djoamersfoort/adjustable-soldering-iron/3D models/Case/Baseplate/Baseplate.png

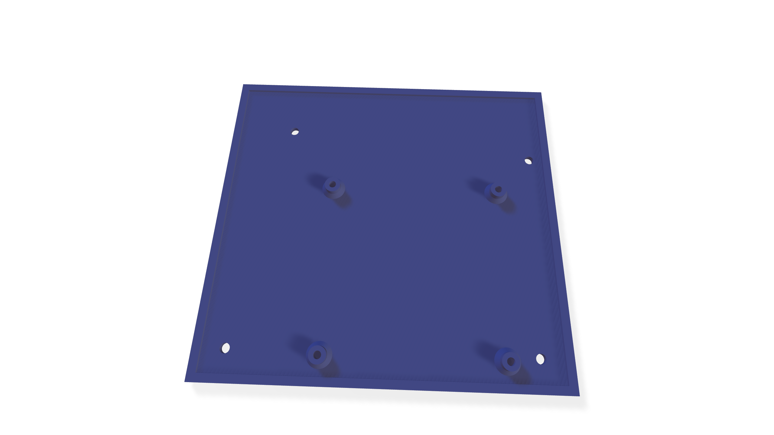
3D models/Case/Baseplate/Baseplate.png
