djoamersfoort/adjustable-soldering-iron/3D models/Case/Feet/Feet-one.png

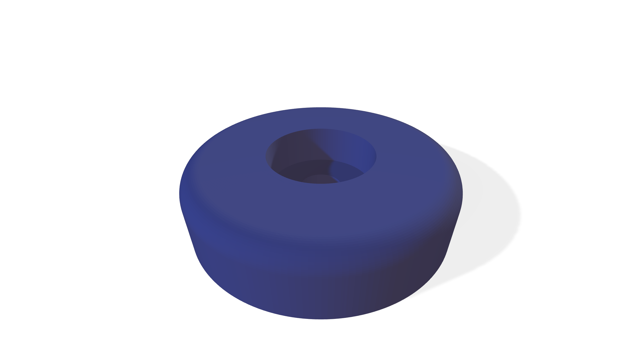
3D models/Case/Feet/Feet-one.png
