djoamersfoort/adjustable-soldering-iron/3D models/Case/IEC320-backplate-for-woodpanels-large/IEC320 backplate-for woodpanels-large.png

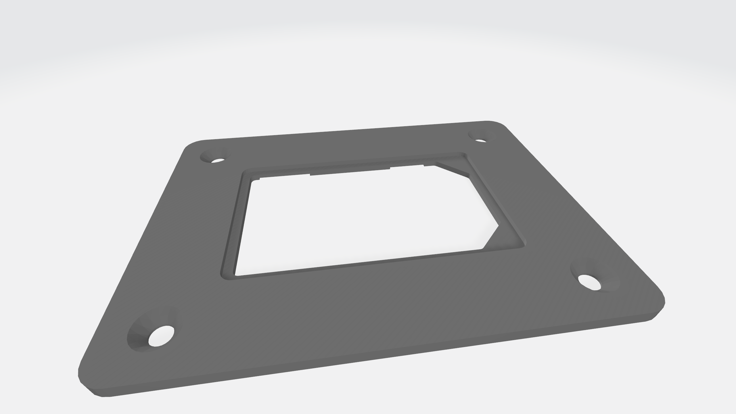
3D models/Case/IEC320-backplate-for-woodpanels-large/IEC320 backplate-for woodpanels-large.png
