djoamersfoort/adjustable-soldering-iron/3D models/Case/Standoff/Standoff-one.png

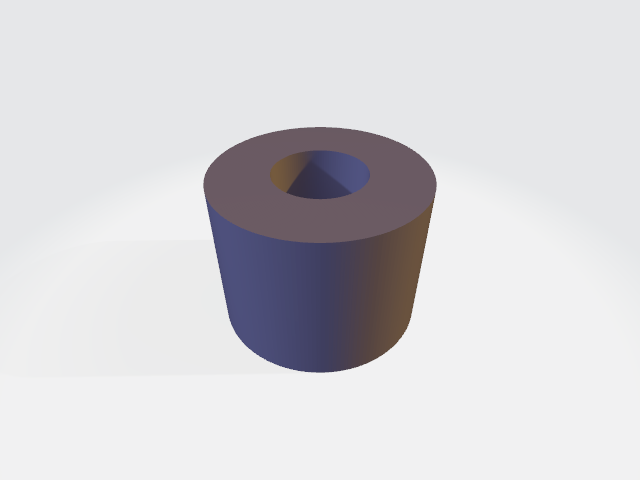
3D models/Case/Standoff/Standoff-one.png
