djoamersfoort/adjustable-soldering-iron/3D models/Parts/4-digit Display/4-digit Display.png

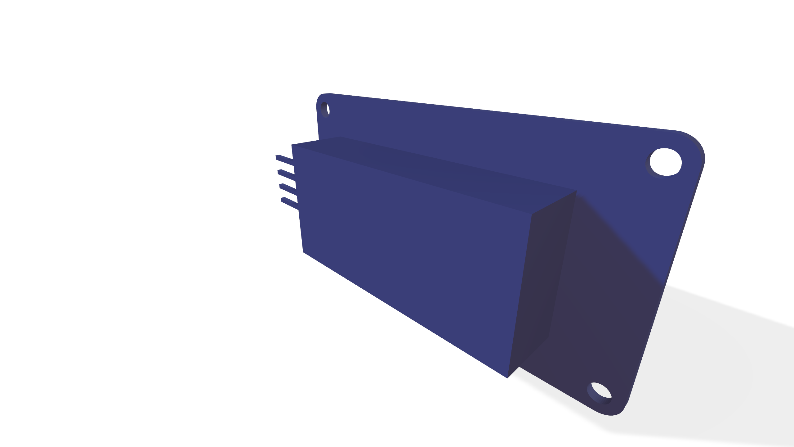
3D models/Parts/4-digit Display/4-digit Display.png
