djoamersfoort/adjustable-soldering-iron/3D models/Parts/LM2596 Place holder/LM2596 Place holder2.JPG

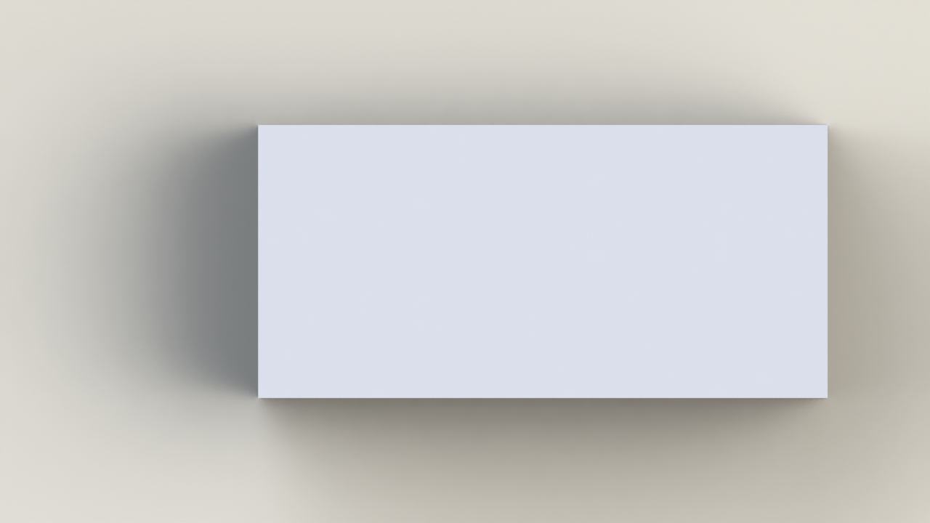
3D models/Parts/LM2596 Place holder/LM2596 Place holder2.JPG
