djoamersfoort/adjustable-soldering-iron/3D models/Parts/LM2596 Place holder/LM2596 Place holder.png

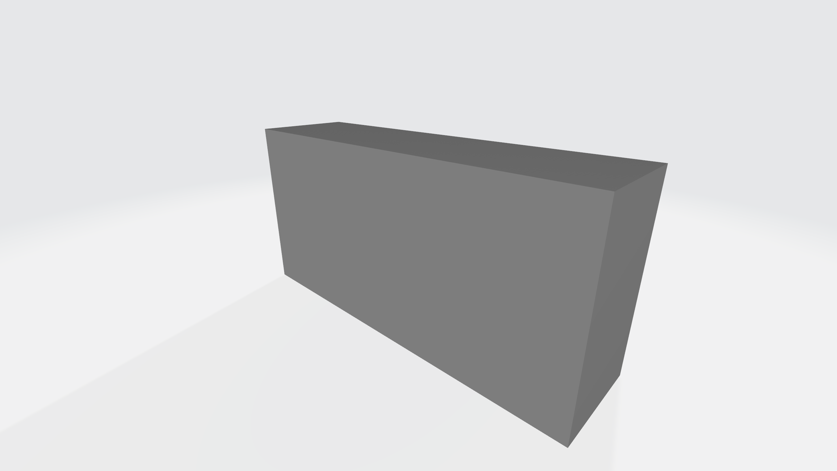
3D models/Parts/LM2596 Place holder/LM2596 Place holder.png
