djoamersfoort/adjustable-soldering-iron/3D models/Parts/MAX6675-K/MAX6675-K.JPG

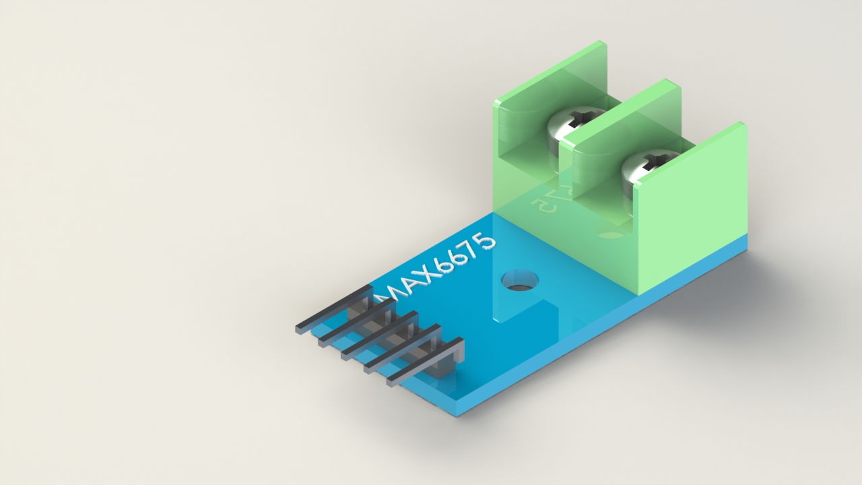
3D models/Parts/MAX6675-K/MAX6675-K.JPG
