djoamersfoort/adjustable-soldering-iron/3D models/Parts/Rotary Encoder/Rotary-Encoder2.JPG

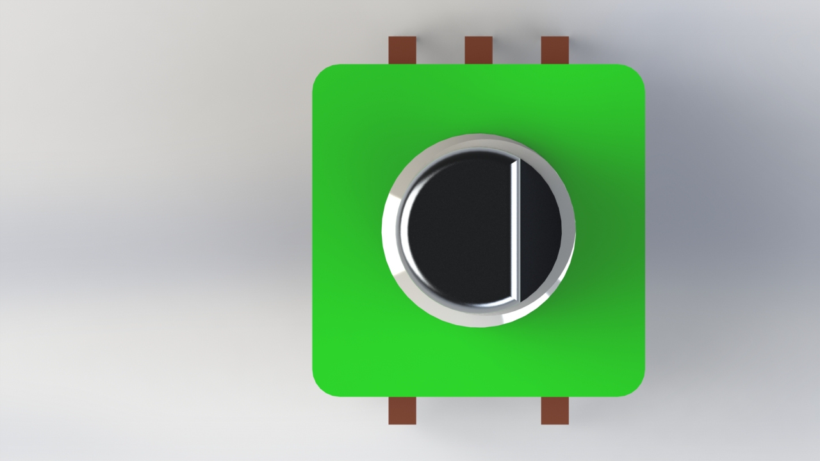
3D models/Parts/Rotary Encoder/Rotary-Encoder2.JPG
