djoamersfoort/adjustable-soldering-iron/3D models/Parts/Rotary Encoder/Rotary-Encoder.JPG

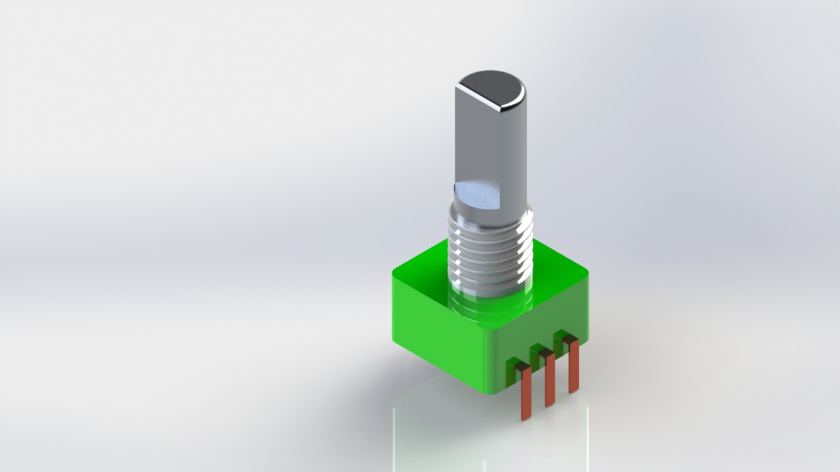
3D models/Parts/Rotary Encoder/Rotary-Encoder.JPG
