djoamersfoort/adjustable-soldering-iron/Box/BoxFront.dxf

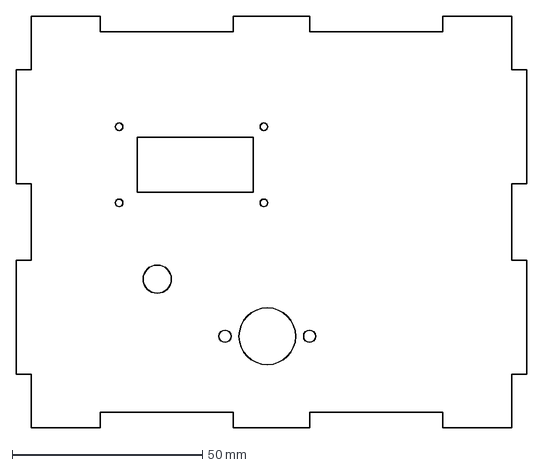
[picture p42: CAD file, 2020-01-24]
Box/BoxFront.dxf
134.0 x 108.0 mm
