djoamersfoort/adjustable-soldering-iron/3D models/Case/Baseplate/Baseplate.stl

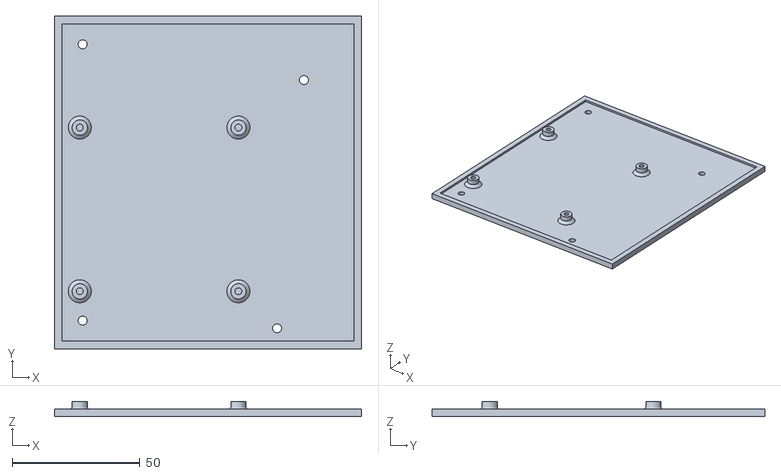
[picture p43: CAD file, 2019-11-08]
3D models/Case/Baseplate/Baseplate.stl
120.0 x 130.0 x 6.00
