djoamersfoort/adjustable-soldering-iron/3D models/Parts/4-digit Display/STEP/STEP Separate parts/Header-Base.STEP

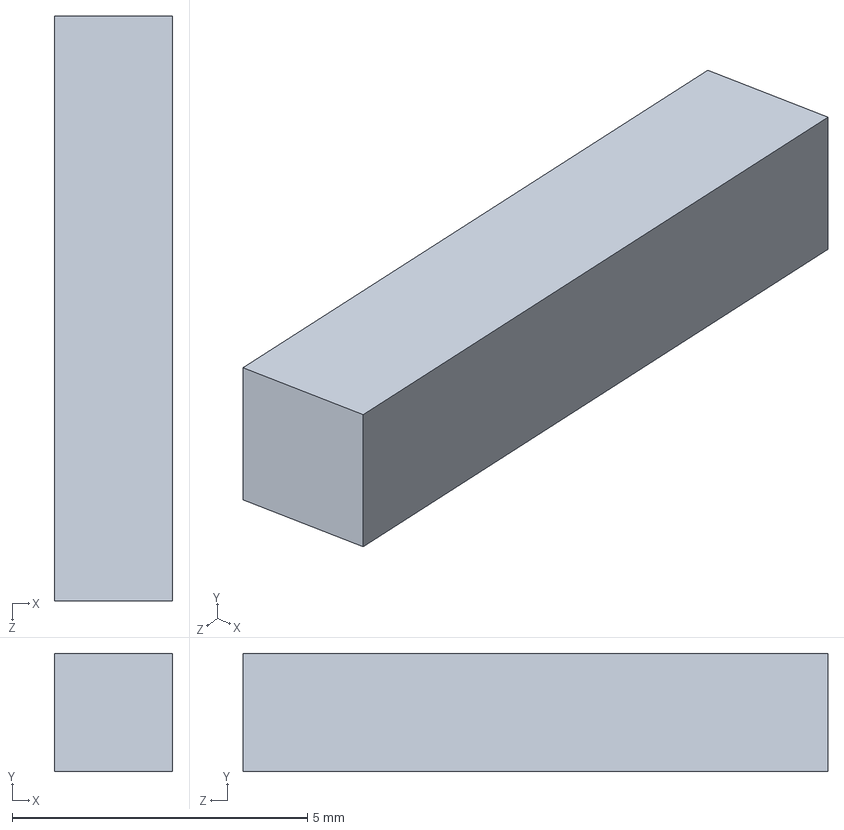
[picture p44: CAD file, 2019-11-08]
3D models/Parts/4-digit Display/STEP/STEP Separate parts/Header-Base.STEP
2.00 x 2.00 x 9.90 mm
