djoamersfoort/adjustable-soldering-iron/3D models/Parts/Rotary Encoder/STEP/STEP Separate parts/Rotary-Encoder knop.STEP

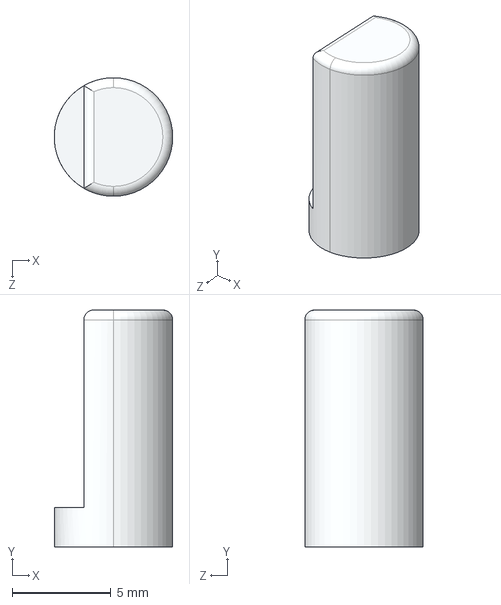
[picture p45: CAD file, 2019-11-08]
3D models/Parts/Rotary Encoder/STEP/STEP Separate parts/Rotary-Encoder knop.STEP
6.00 x 12.0 x 6.00 mm
