djoamersfoort/adjustable-soldering-iron/Box/BoxLeft.dxf

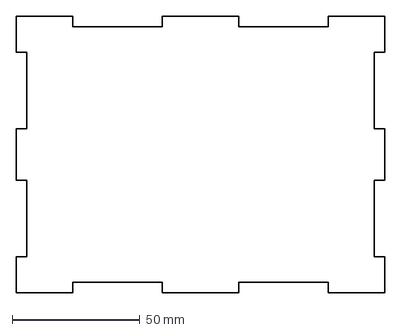
[picture p46: CAD file, 2020-01-24]
Box/BoxLeft.dxf
144.0 x 108.0 mm
