djoamersfoort/adjustable-soldering-iron/3D models/Parts/MAX6675-K/STEP/STEP Separate parts/MAX6675-K PCB.STEP

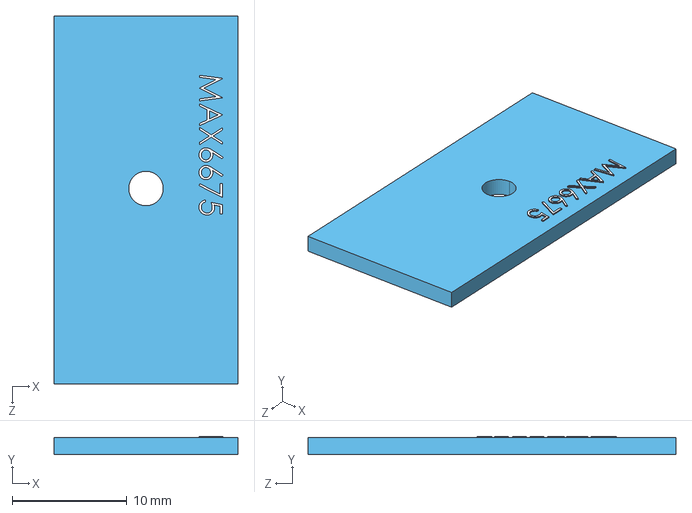
[picture p47: CAD file, 2019-11-08]
3D models/Parts/MAX6675-K/STEP/STEP Separate parts/MAX6675-K PCB.STEP
16.0 x 1.60 x 32.0 mm
