djoamersfoort/adjustable-soldering-iron/3D models/Parts/PSU/STEP/STEP Separate parts/conntectorblock.STEP

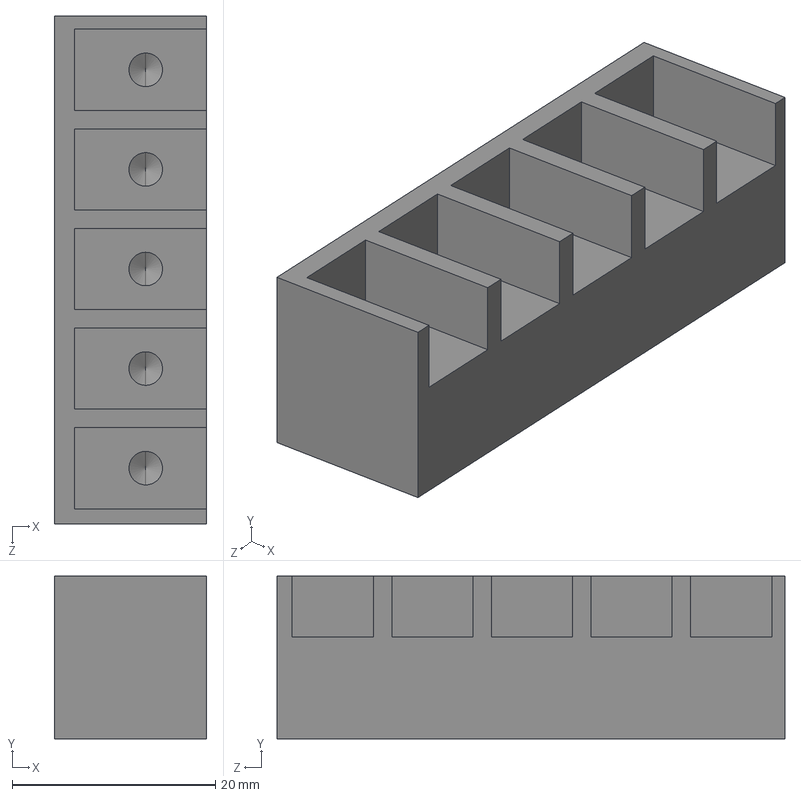
[picture p48: CAD file, 2019-11-08]
3D models/Parts/PSU/STEP/STEP Separate parts/conntectorblock.STEP
15.0 x 16.0 x 50.0 mm
