djoamersfoort/adjustable-soldering-iron/3D models/Parts/Rotary Encoder/STEP/STEP Separate parts/Rotary-Encoder Pin.STEP

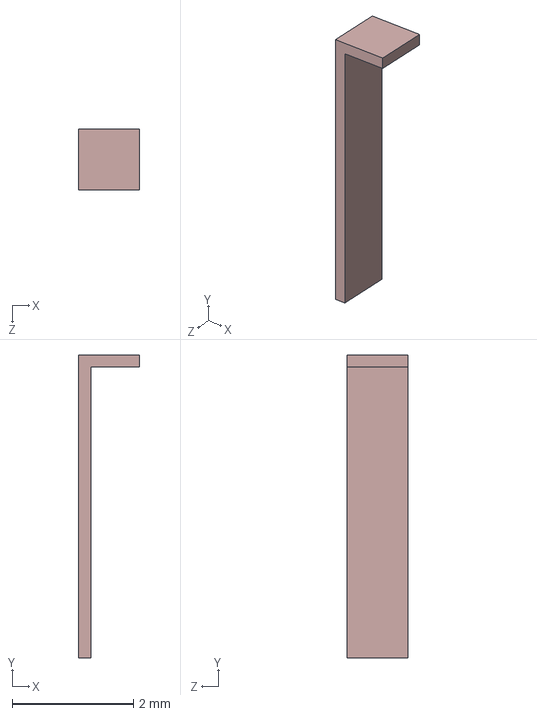
[picture p49: CAD file, 2019-11-08]
3D models/Parts/Rotary Encoder/STEP/STEP Separate parts/Rotary-Encoder Pin.STEP
1.00 x 5.00 x 1.00 mm
