djoamersfoort/adjustable-soldering-iron/Box/BoxRight.dxf

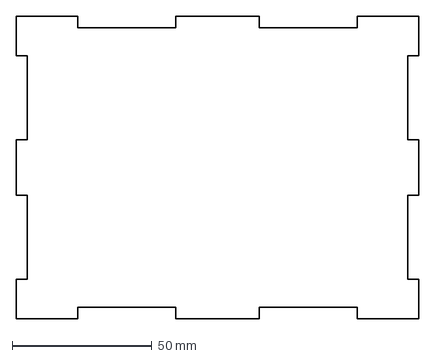
[picture p50: CAD file, 2020-01-24]
Box/BoxRight.dxf
144.0 x 108.0 mm
