djoamersfoort/adjustable-soldering-iron/3D models/Parts/4-digit Display/STEP/STEP Separate parts/Header.STEP

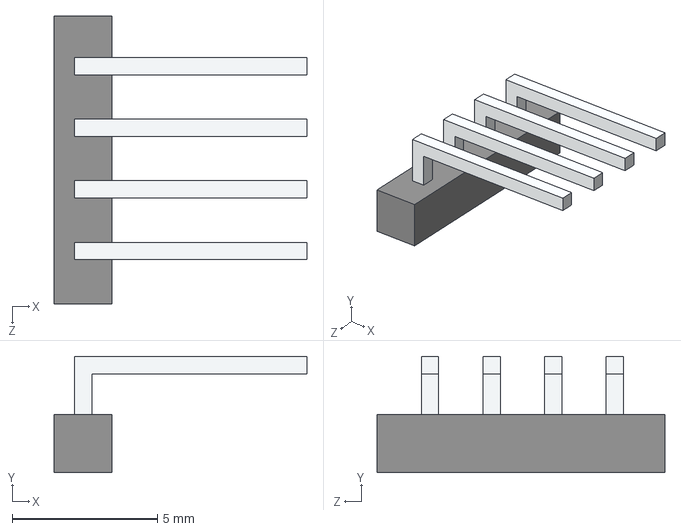
[picture p51: CAD file, 2019-11-08]
3D models/Parts/4-digit Display/STEP/STEP Separate parts/Header.STEP
8.70 x 4.00 x 9.90 mm
Header-Base
Header-Pin x 4
