djoamersfoort/adjustable-soldering-iron/3D models/Parts/MAX6675-K/STEP/STEP Separate parts/Header-Base.STEP

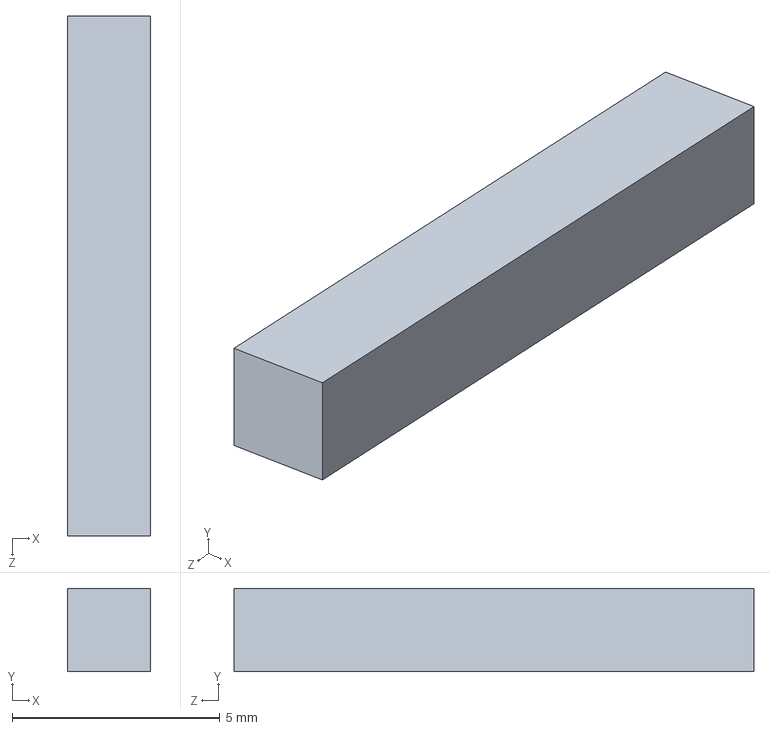
[picture p52: CAD file, 2019-11-08]
3D models/Parts/MAX6675-K/STEP/STEP Separate parts/Header-Base.STEP
2.00 x 2.00 x 12.5 mm
