djoamersfoort/adjustable-soldering-iron/Box/BoxBottom.dxf

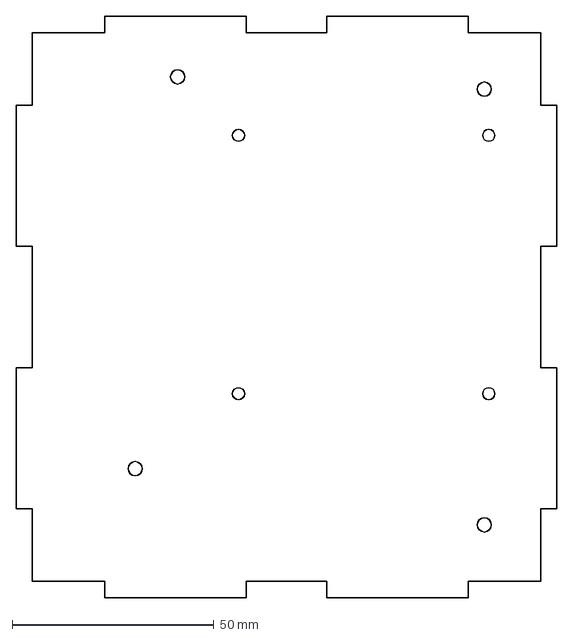
[picture p53: CAD file, 2020-01-24]
Box/BoxBottom.dxf
134.0 x 144.0 mm
