djoamersfoort/adjustable-soldering-iron/3D models/Parts/4-digit Display/STEP/STEP Separate parts/PCB.STEP

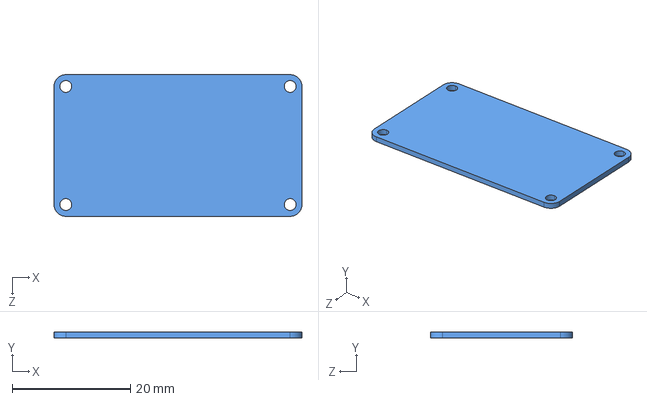
[picture p54: CAD file, 2019-11-08]
3D models/Parts/4-digit Display/STEP/STEP Separate parts/PCB.STEP
42.0 x 1.00 x 24.0 mm
