djoamersfoort/adjustable-soldering-iron/3D models/Parts/MAX6675-K/STEP/STEP Separate parts/MAX6675-K Connector-Block Base.STEP

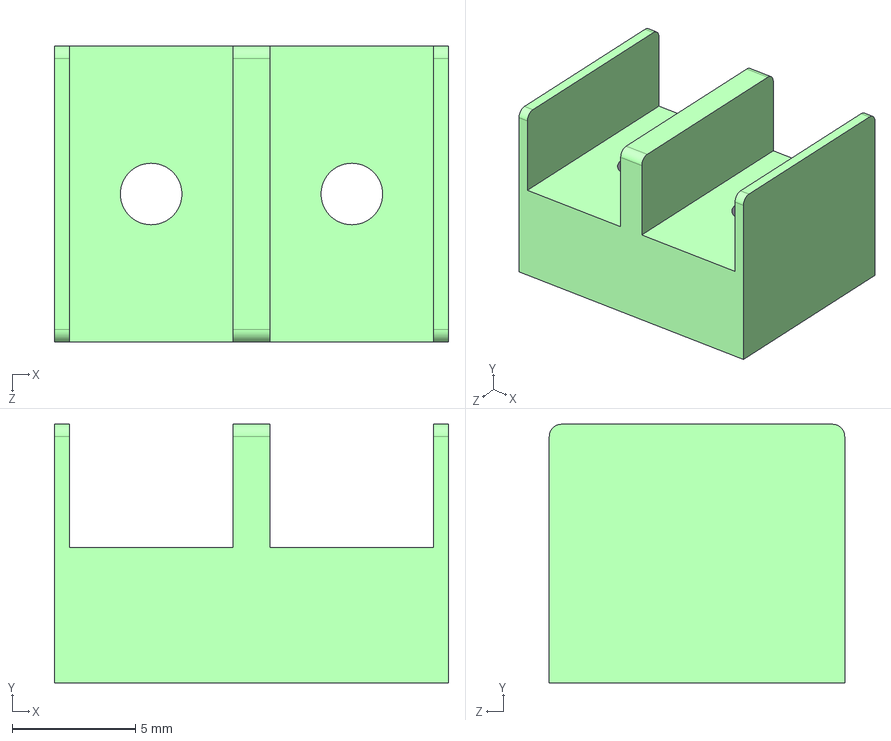
[picture p55: CAD file, 2019-11-08]
3D models/Parts/MAX6675-K/STEP/STEP Separate parts/MAX6675-K Connector-Block Base.STEP
16.0 x 10.5 x 12.0 mm
