djoamersfoort/adjustable-soldering-iron/Box/BoxBack.dxf

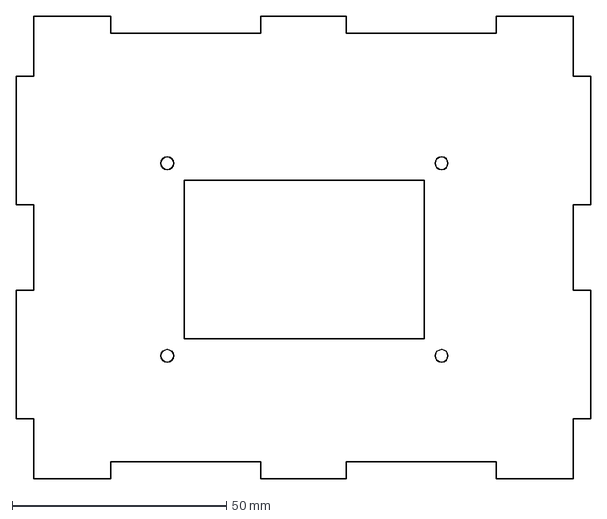
[picture p56: CAD file, 2020-01-24]
Box/BoxBack.dxf
134.0 x 108.0 mm
