djoamersfoort/adjustable-soldering-iron/Box/BoxTop.dxf

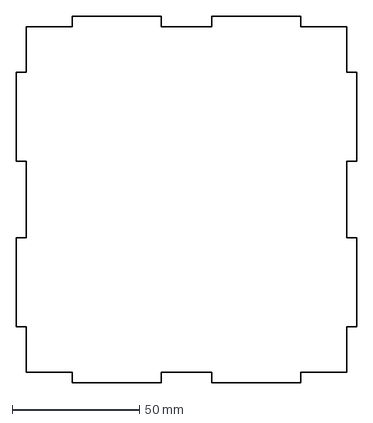
[picture p57: CAD file, 2020-01-24]
Box/BoxTop.dxf
134.0 x 144.0 mm
