djoamersfoort/adjustable-soldering-iron/3D models/Parts/PSU/PSU Assembly2.JPG

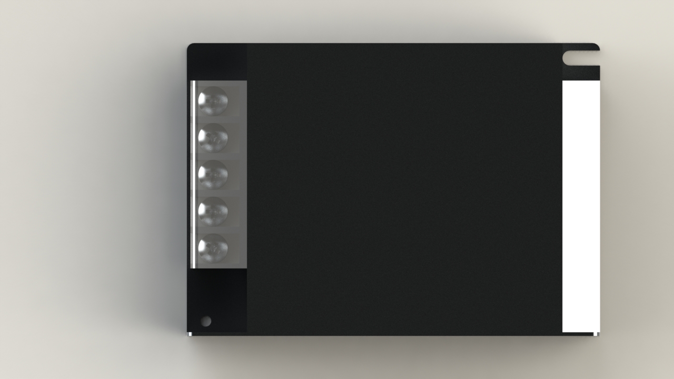
3D models/Parts/PSU/PSU Assembly2.JPG
