djoamersfoort/adjustable-soldering-iron/3D models/Parts/PSU/PSU Assembly.JPG

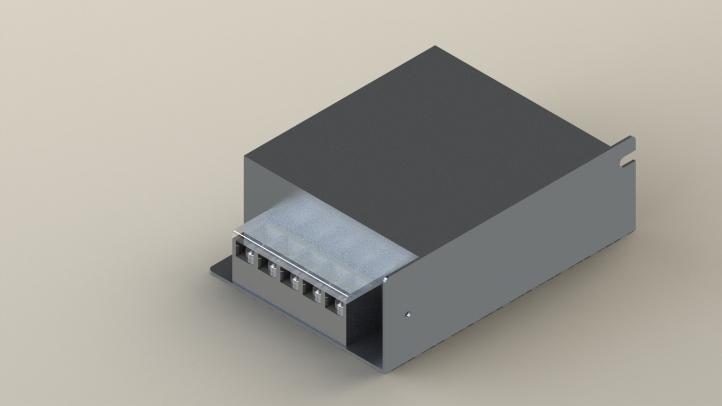
3D models/Parts/PSU/PSU Assembly.JPG
