djoamersfoort/adjustable-soldering-iron/3D models/Parts/PSU/PSU Assembly.png

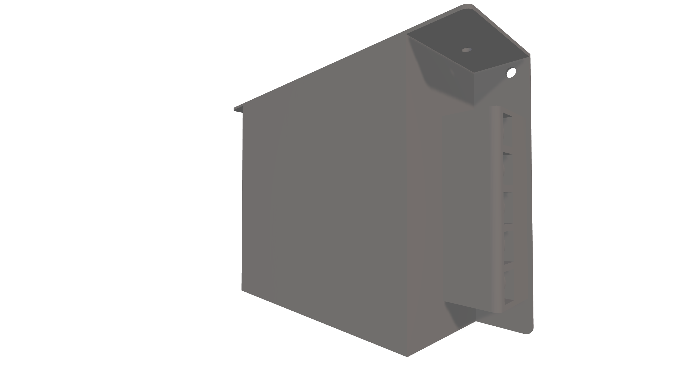
3D models/Parts/PSU/PSU Assembly.png
